o7-machinehum/ovrdrive-v2/src/msc_read.h

/* msc_read.h - MSC READ10 data transfer
 *
 * SPDX-License-Identifier: Apache-2.0
 */
#ifndef MSC_READ_H_
#define MSC_READ_H_

#include "bot_state.h"

void msc_read_sectors(void);

#endif /* MSC_READ_H_ */
