o7-machinehum/ovrdrive-v2/src/msc_write.h

/* msc_write.h - MSC WRITE10 data transfer
 *
 * SPDX-License-Identifier: Apache-2.0
 */
#ifndef MSC_WRITE_H_
#define MSC_WRITE_H_

#include "bot_state.h"

void msc_write_sectors(void);

#endif /* MSC_WRITE_H_ */
