o7-machinehum/ovrdrive-v2/src/sw_udisk.h

/* sw_udisk.h - BSP compatibility shim
 *
 * The BSP USB ISR files (CH56x_usb20_devbulk.c, CH56x_usb30_devbulk.c)
 * include this header. It re-exports the new module headers they need.
 *
 * SPDX-License-Identifier: Apache-2.0
 */
#ifndef SW_UDISK_H_
#define SW_UDISK_H_

#include "bot_state.h"
#include "bot.h"

#endif /* SW_UDISK_H_ */
